Blue-Net-Team/2024-GuangDong-Engineering-practice-and-innovation-ability-competition---Don-t-count-on-us/Pic/1.png

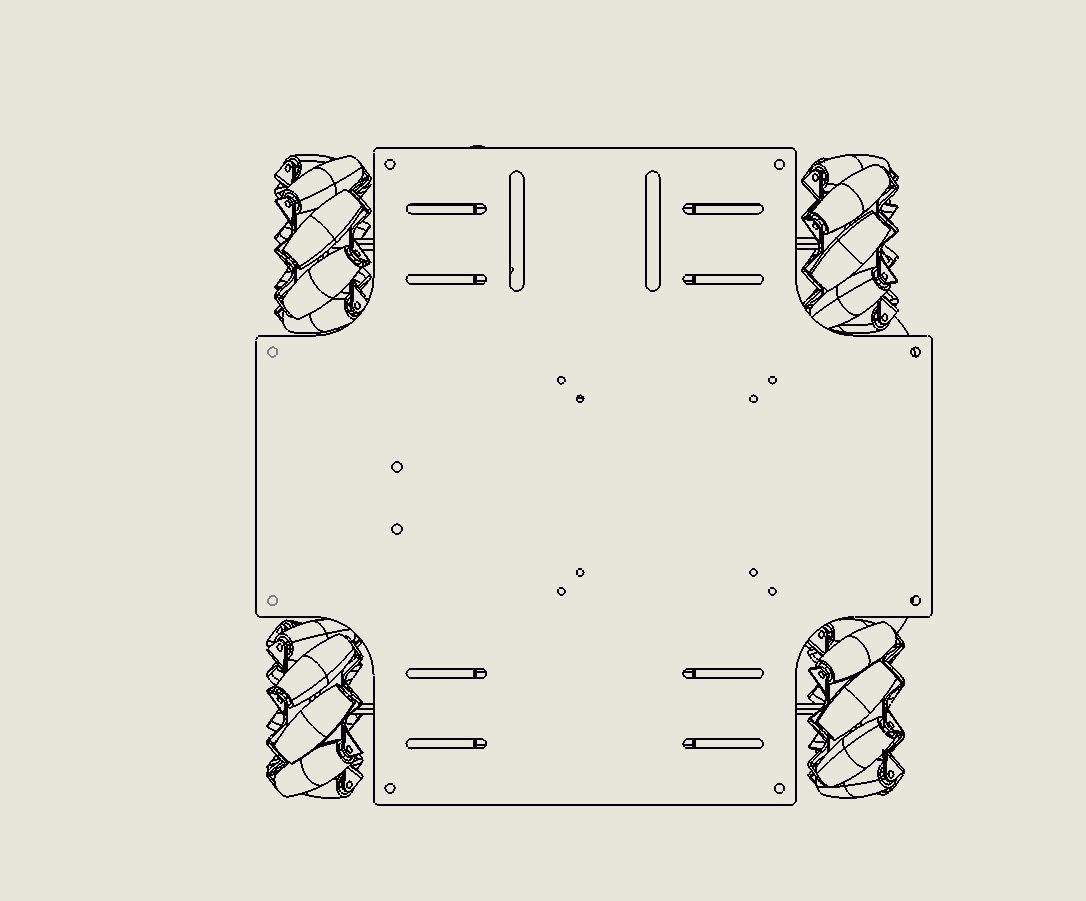
Pic/1.png
