Blue-Net-Team/2024-GuangDong-Engineering-practice-and-innovation-ability-competition---Don-t-count-on-us/Pic/3.png

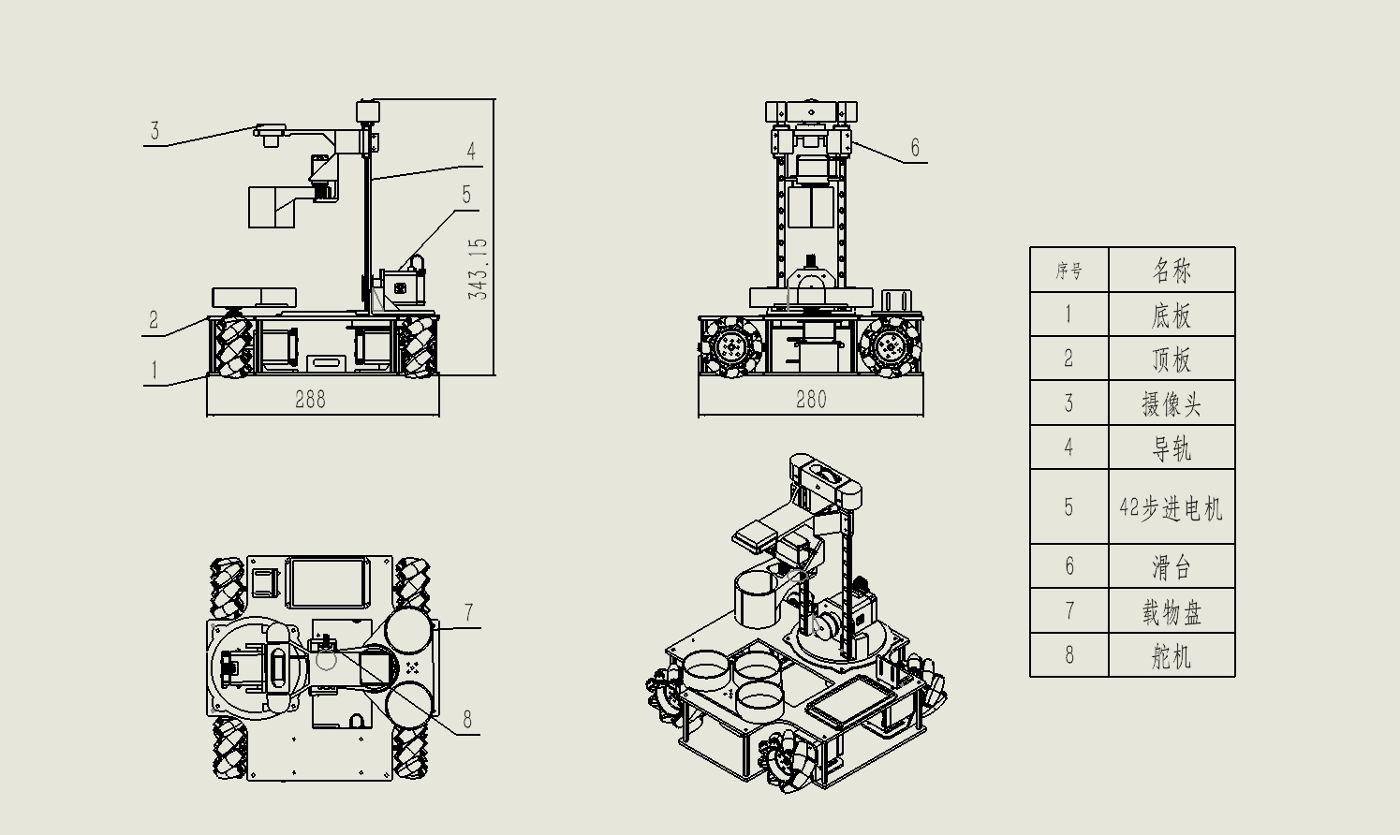
Pic/3.png
