Blue-Net-Team/2024-GuangDong-Engineering-practice-and-innovation-ability-competition---Don-t-count-on-us/Structure/MGN9-250.SLDASM

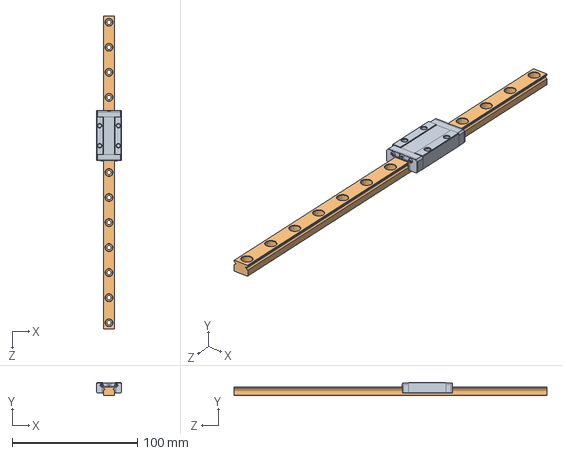
[picture p6: CAD file, 2024-07-28]
Structure/MGN9-250.SLDASM
20.0 x 10.0 x 250.0 mm
滑轨
滑台
