Blue-Net-Team/2024-GuangDong-Engineering-practice-and-innovation-ability-competition---Don-t-count-on-us/Structure/同步轮.SLDPRT

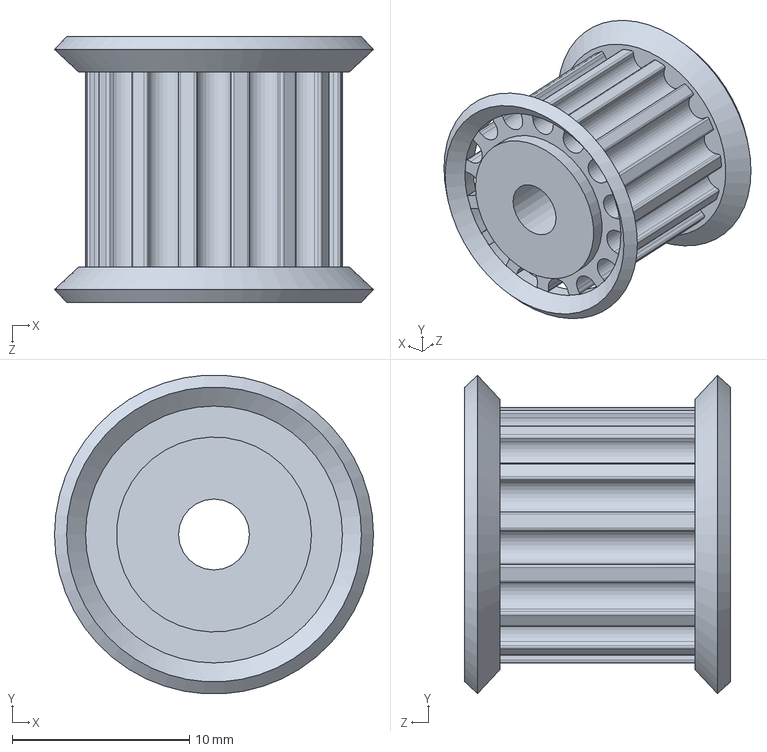
[picture p20: CAD file, 2024-07-28]
Structure/同步轮.SLDPRT
18.0 x 18.0 x 15.0 mm
