Blue-Net-Team/2024-GuangDong-Engineering-practice-and-innovation-ability-competition---Don-t-count-on-us/Structure/便携爪子初始加长.SLDPRT

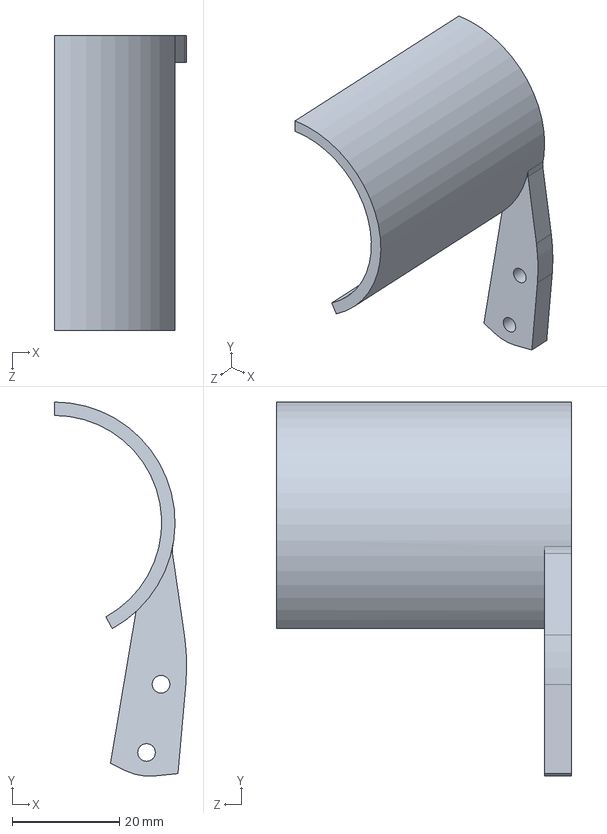
[picture p21: CAD file, 2024-07-28]
Structure/便携爪子初始加长.SLDPRT
24.7 x 69.7 x 55.0 mm
