Blue-Net-Team/2024-GuangDong-Engineering-practice-and-innovation-ability-competition---Don-t-count-on-us/Structure/轴承.SLDPRT

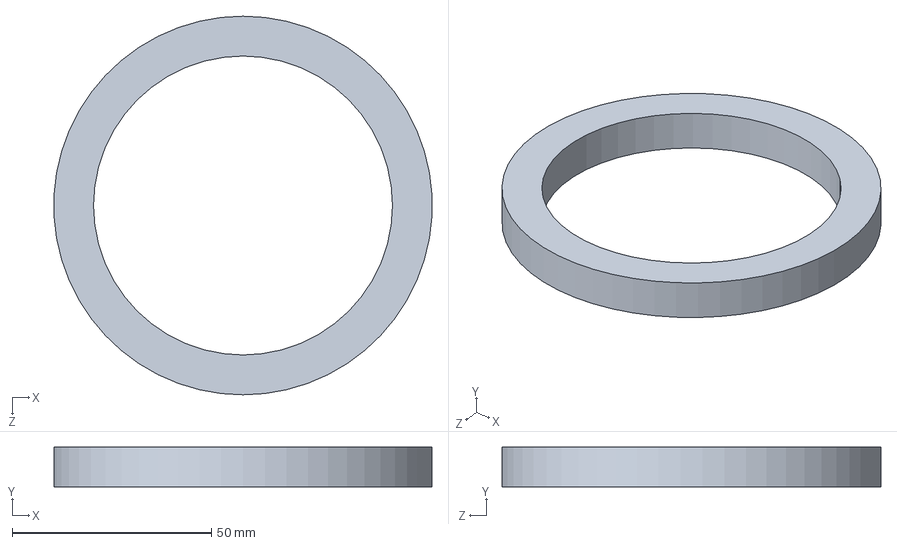
[picture p22: CAD file, 2024-07-28]
Structure/轴承.SLDPRT
94.8 x 10.0 x 95.0 mm
