Blue-Net-Team/2024-GuangDong-Engineering-practice-and-innovation-ability-competition---Don-t-count-on-us/Structure/爪子2.SLDPRT

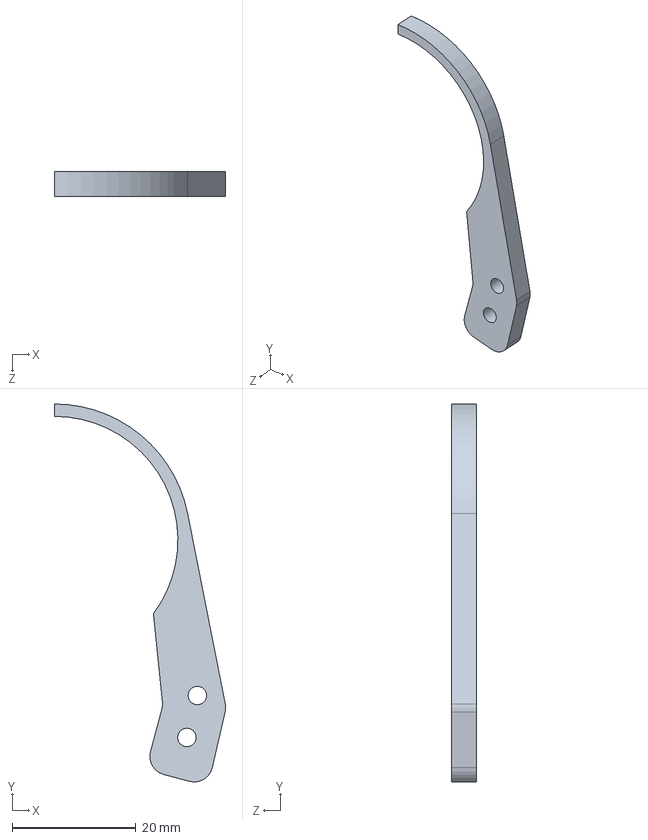
[picture p24: CAD file, 2024-07-28]
Structure/爪子2.SLDPRT
27.7 x 61.2 x 4.00 mm
