Blue-Net-Team/2024-GuangDong-Engineering-practice-and-innovation-ability-competition---Don-t-count-on-us/Structure/电池支架2.SLDPRT

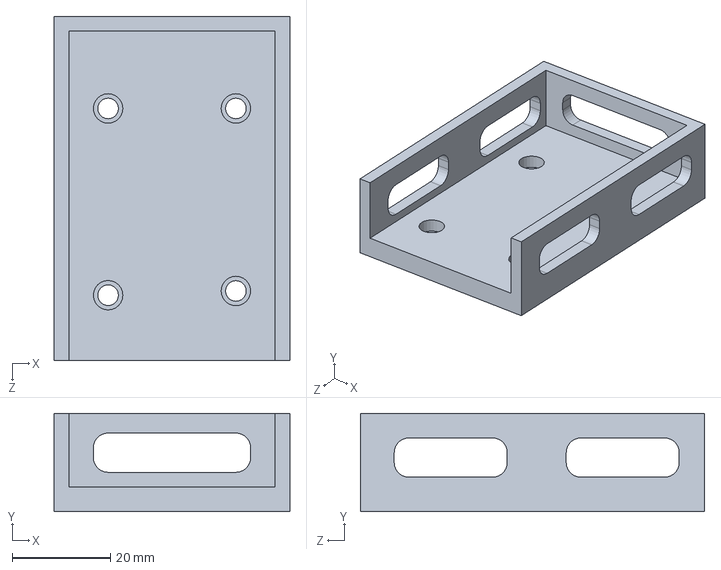
[picture p25: CAD file, 2024-07-28]
Structure/电池支架2.SLDPRT
48.0 x 20.0 x 70.0 mm
