Blue-Net-Team/2024-GuangDong-Engineering-practice-and-innovation-ability-competition---Don-t-count-on-us/Structure/上板.SLDPRT

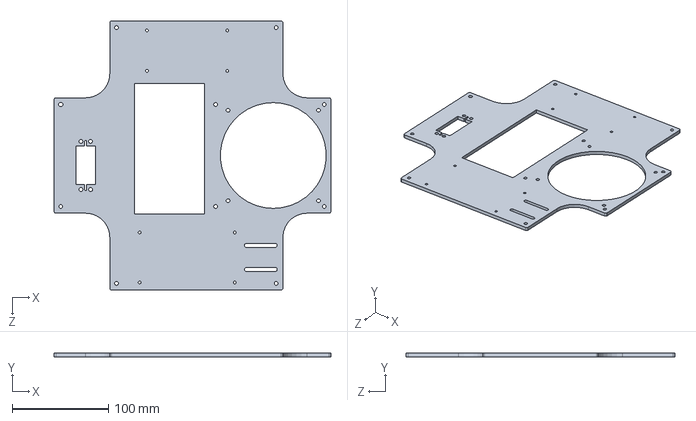
[picture p26: CAD file, 2024-07-28]
Structure/上板.SLDPRT
288.0 x 4.00 x 280.0 mm
