Blue-Net-Team/2024-GuangDong-Engineering-practice-and-innovation-ability-competition---Don-t-count-on-us/Structure/便携爪子初始.SLDPRT

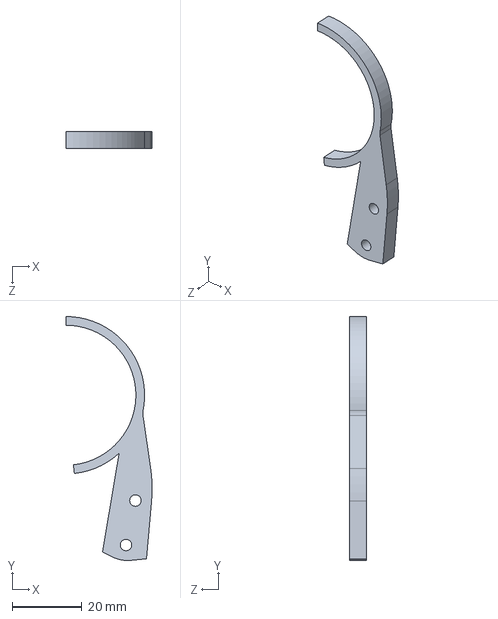
[picture p27: CAD file, 2024-07-28]
Structure/便携爪子初始.SLDPRT
24.6 x 69.7 x 5.00 mm
