Blue-Net-Team/2024-GuangDong-Engineering-practice-and-innovation-ability-competition---Don-t-count-on-us/Structure/云台顶盘.SLDPRT

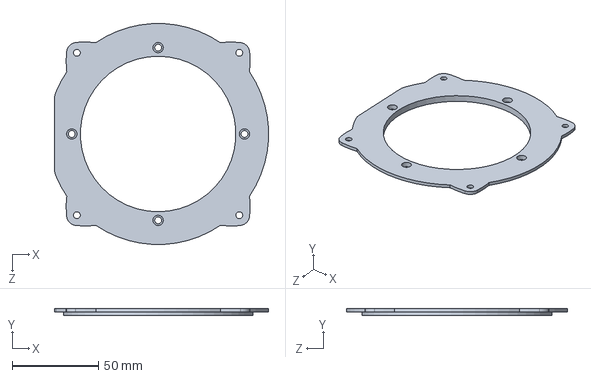
[picture p28: CAD file, 2024-07-28]
Structure/云台顶盘.SLDPRT
123.9 x 4.00 x 127.8 mm
