Blue-Net-Team/2024-GuangDong-Engineering-practice-and-innovation-ability-competition---Don-t-count-on-us/Structure/摄像头固定支架.SLDPRT

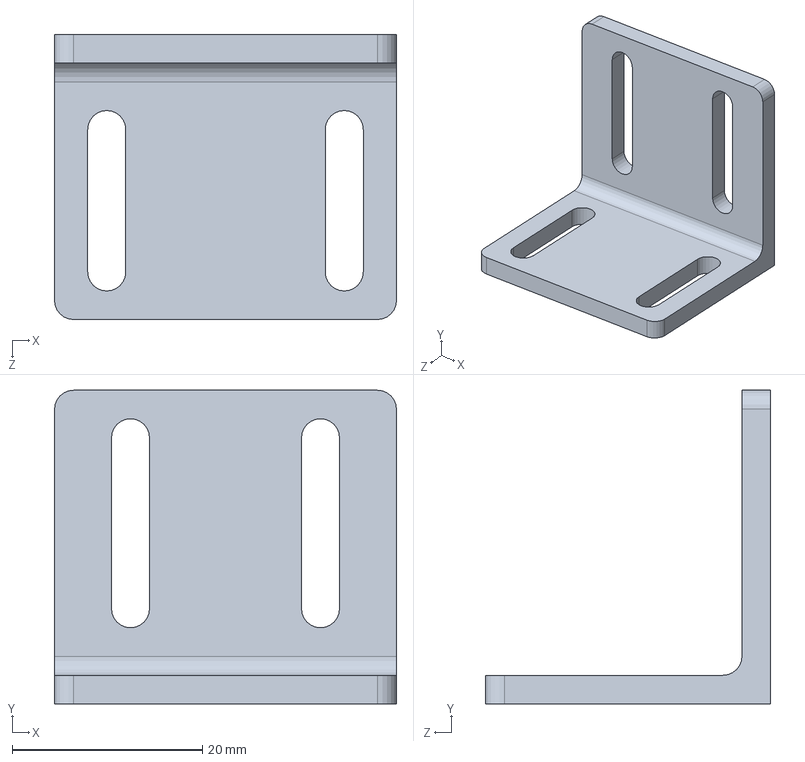
[picture p29: CAD file, 2024-07-28]
Structure/摄像头固定支架.SLDPRT
36.0 x 33.0 x 30.0 mm
