Blue-Net-Team/2024-GuangDong-Engineering-practice-and-innovation-ability-competition---Don-t-count-on-us/Structure/舵机.SLDPRT

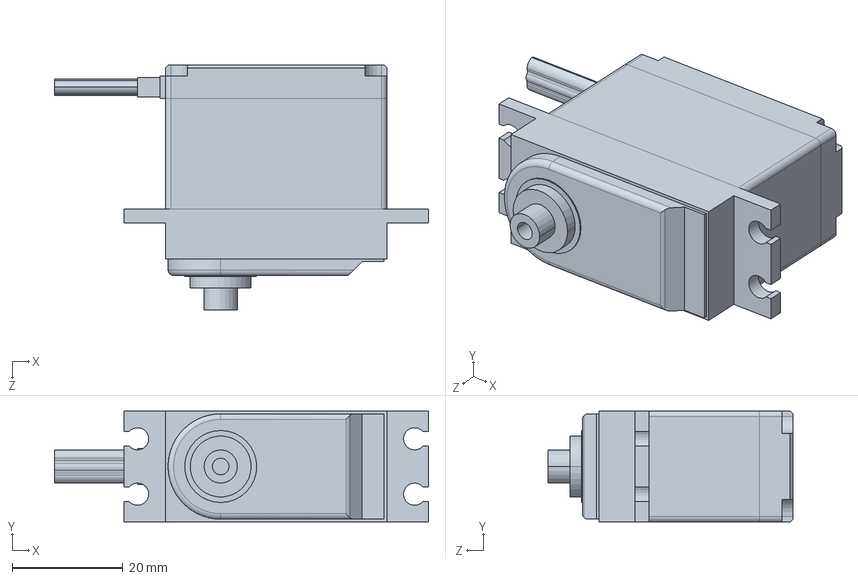
[picture p30: CAD file, 2024-07-28]
Structure/舵机.SLDPRT
67.5 x 20.0 x 44.2 mm
