Blue-Net-Team/2024-GuangDong-Engineering-practice-and-innovation-ability-competition---Don-t-count-on-us/Structure/树莓派固定2.SLDPRT

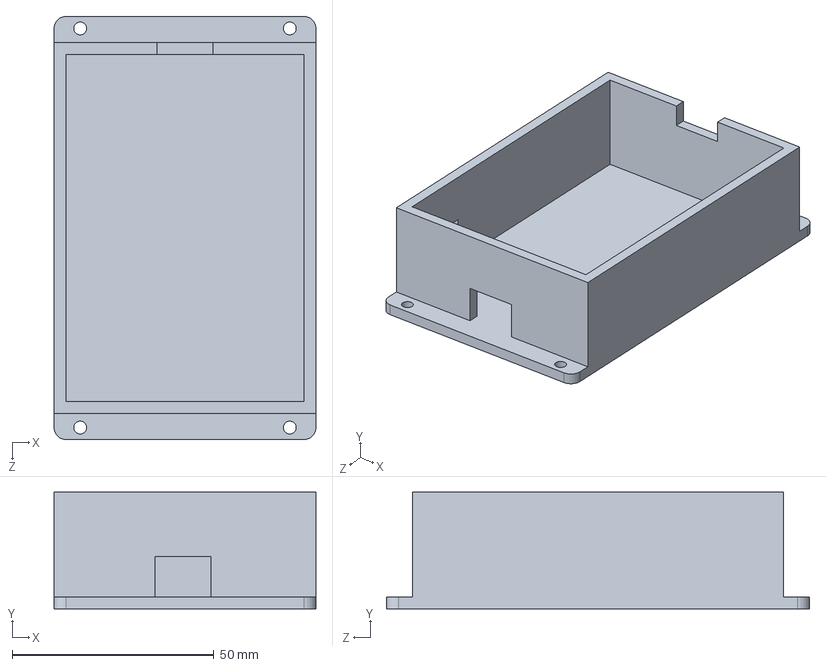
[picture p31: CAD file, 2024-07-28]
Structure/树莓派固定2.SLDPRT
65.0 x 29.0 x 105.0 mm
