Blue-Net-Team/2024-GuangDong-Engineering-practice-and-innovation-ability-competition---Don-t-count-on-us/Structure/下固定板.SLDPRT

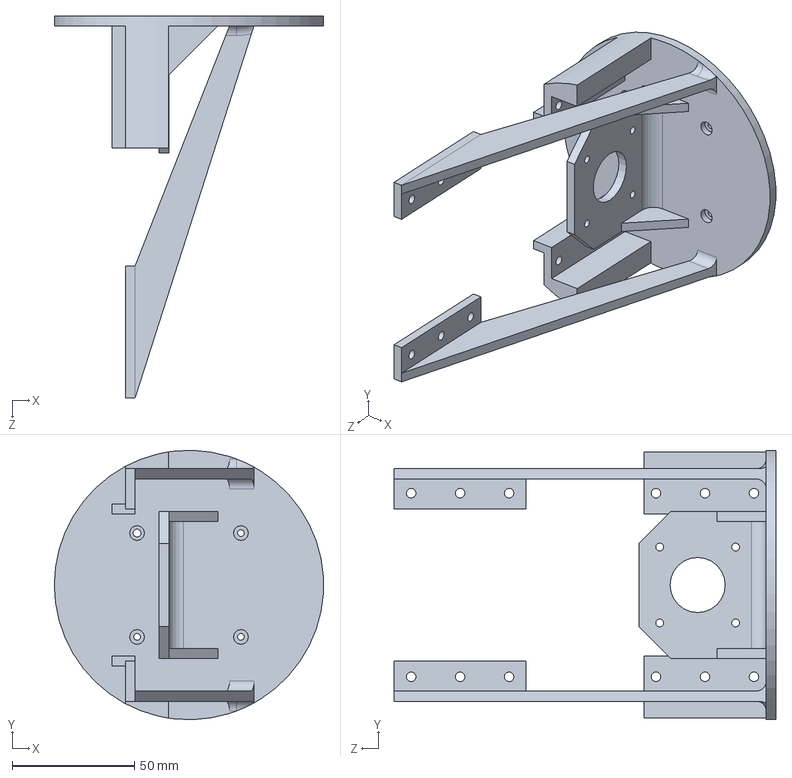
[picture p32: CAD file, 2024-07-28]
Structure/下固定板.SLDPRT
110.0 x 109.9 x 156.0 mm
