Blue-Net-Team/2024-GuangDong-Engineering-practice-and-innovation-ability-competition---Don-t-count-on-us/Structure/机械爪右便携支架.SLDPRT

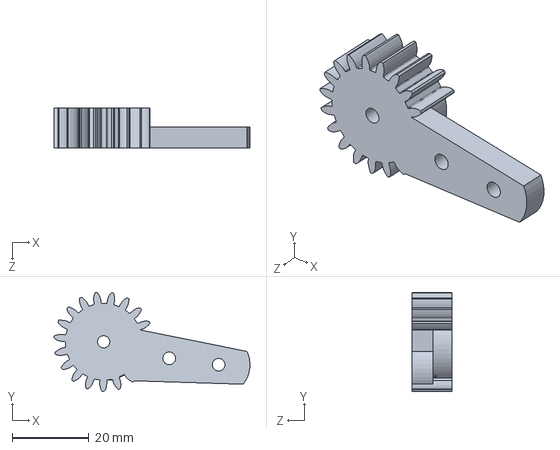
[picture p33: CAD file, 2024-07-28]
Structure/机械爪右便携支架.SLDPRT
51.1 x 25.9 x 10.4 mm
