Blue-Net-Team/2024-GuangDong-Engineering-practice-and-innovation-ability-competition---Don-t-count-on-us/Structure/上同步轮固定.SLDPRT

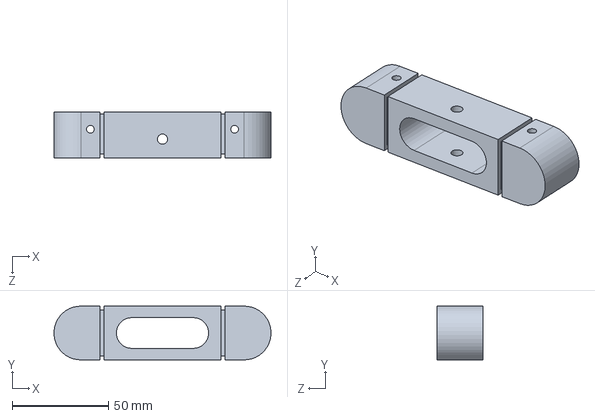
[picture p34: CAD file, 2024-07-28]
Structure/上同步轮固定.SLDPRT
112.9 x 28.0 x 24.0 mm
