Blue-Net-Team/2024-GuangDong-Engineering-practice-and-innovation-ability-competition---Don-t-count-on-us/Structure/底板.SLDPRT

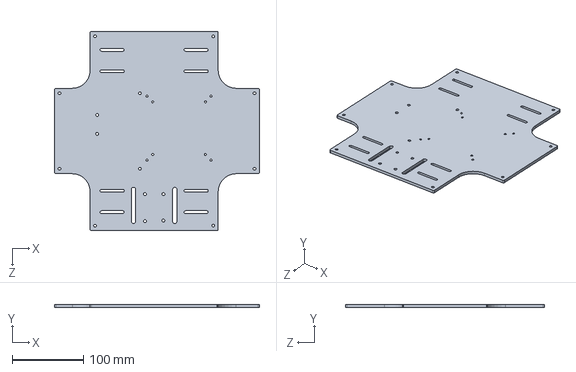
[picture p35: CAD file, 2024-07-28]
Structure/底板.SLDPRT
288.0 x 4.00 x 280.0 mm
