Blue-Net-Team/2024-GuangDong-Engineering-practice-and-innovation-ability-competition---Don-t-count-on-us/Structure/滑台.SLDPRT

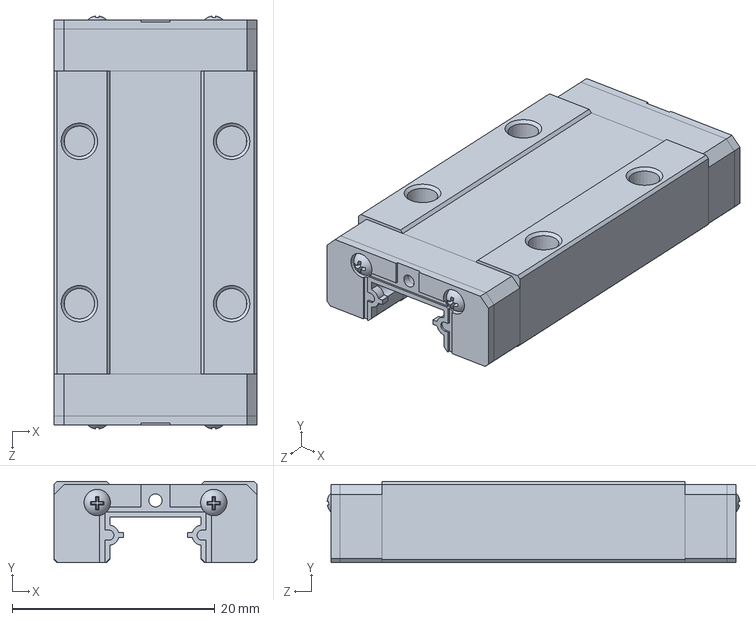
[picture p36: CAD file, 2024-07-28]
Structure/滑台.SLDPRT
20.0 x 8.00 x 40.7 mm
