Blue-Net-Team/2024-GuangDong-Engineering-practice-and-innovation-ability-competition---Don-t-count-on-us/Structure/机械爪左初始.SLDPRT

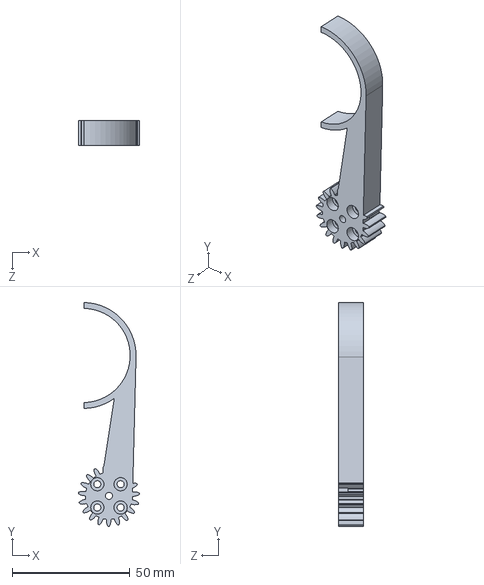
[picture p37: CAD file, 2024-07-28]
Structure/机械爪左初始.SLDPRT
25.9 x 95.1 x 10.5 mm
