Blue-Net-Team/2024-GuangDong-Engineering-practice-and-innovation-ability-competition---Don-t-count-on-us/Structure/升降链接6.SLDPRT

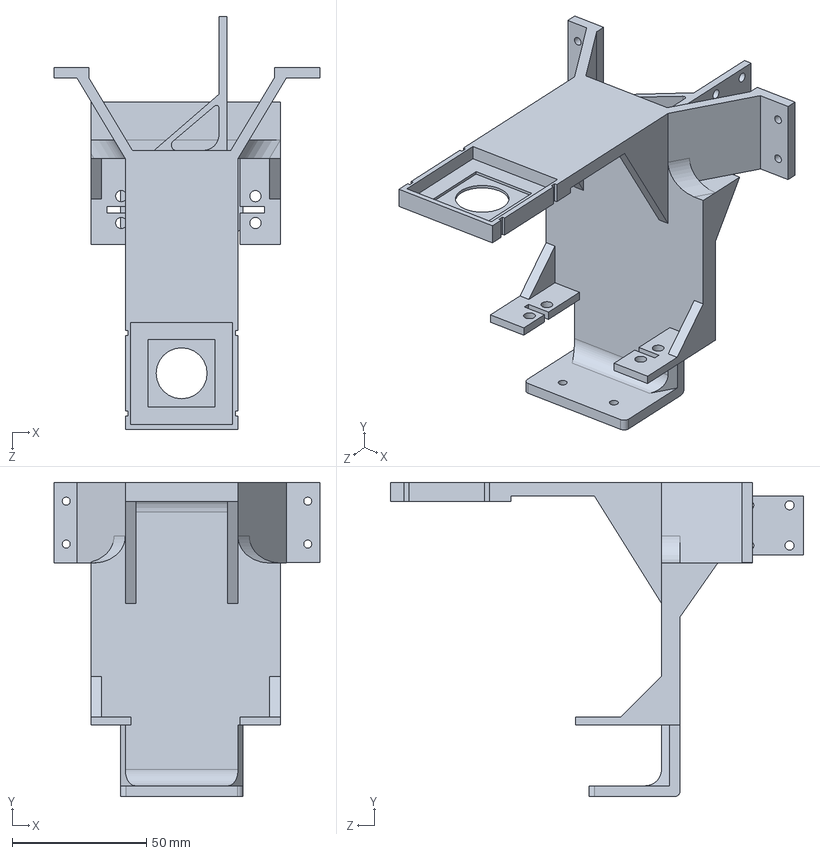
[picture p38: CAD file, 2024-07-28]
Structure/升降链接6.SLDPRT
99.0 x 117.0 x 154.0 mm
