Blue-Net-Team/2024-GuangDong-Engineering-practice-and-innovation-ability-competition---Don-t-count-on-us/Structure/二维码模块固定板.SLDPRT

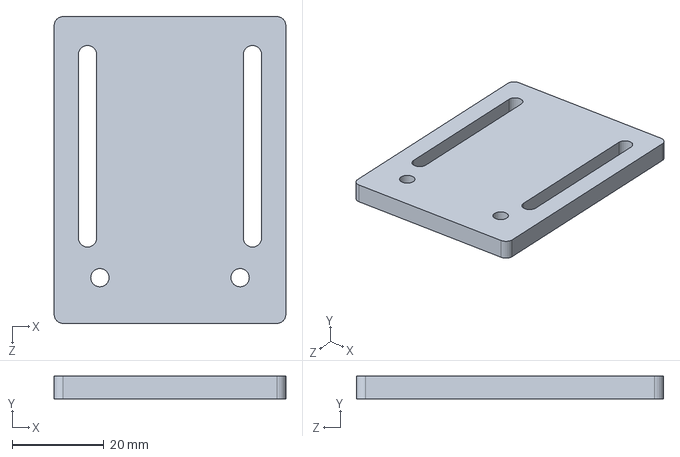
[picture p39: CAD file, 2024-07-28]
Structure/二维码模块固定板.SLDPRT
50.6 x 5.00 x 67.0 mm
