Blue-Net-Team/2024-GuangDong-Engineering-practice-and-innovation-ability-competition---Don-t-count-on-us/Structure/机械爪右初始.SLDPRT

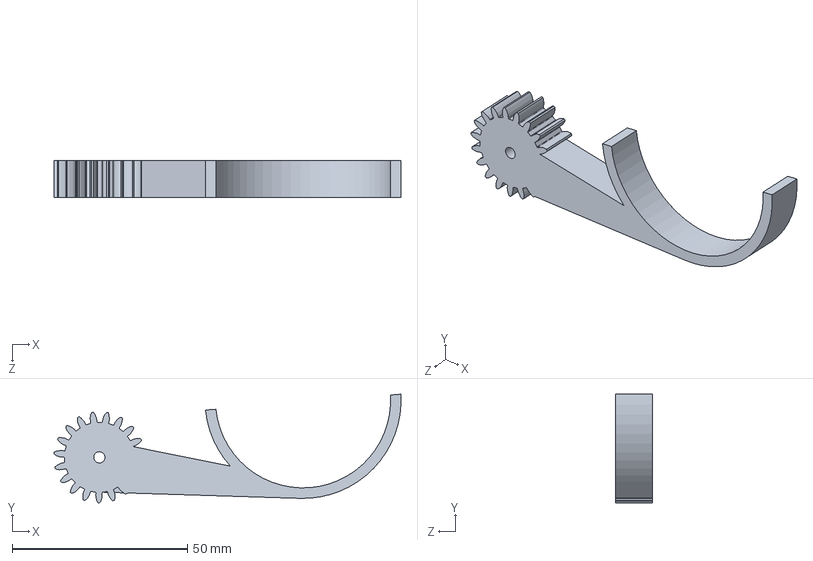
[picture p40: CAD file, 2024-07-28]
Structure/机械爪右初始.SLDPRT
99.1 x 31.0 x 10.4 mm
