Blue-Net-Team/2024-GuangDong-Engineering-practice-and-innovation-ability-competition---Don-t-count-on-us/Structure/二维码模块上层固定架2.SLDPRT

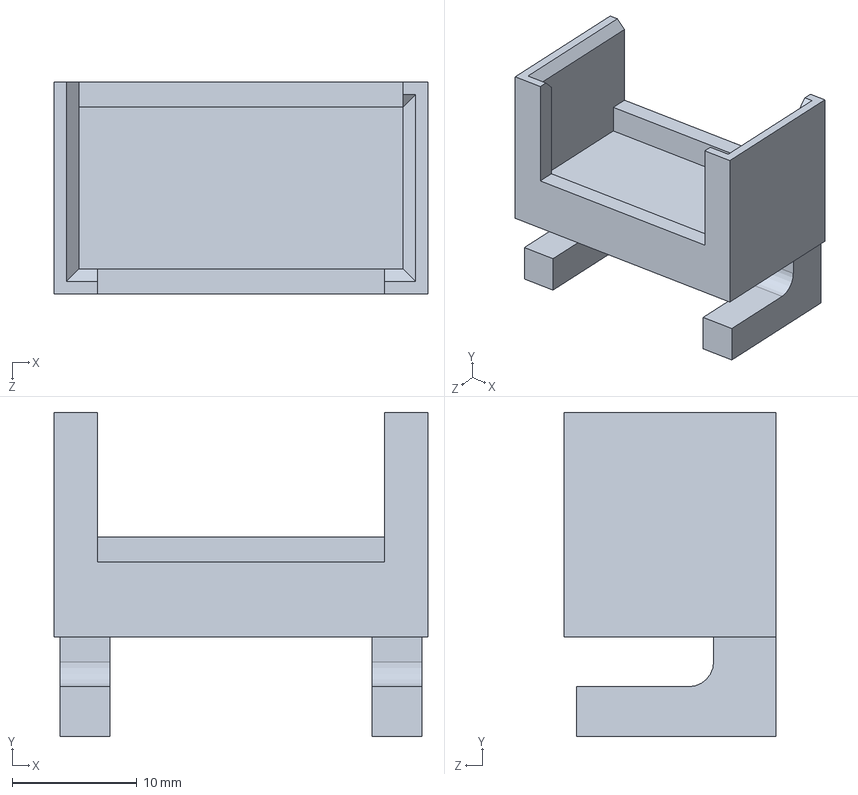
[picture p41: CAD file, 2024-07-28]
Structure/二维码模块上层固定架2.SLDPRT
30.0 x 26.0 x 17.0 mm
