Blue-Net-Team/2024-GuangDong-Engineering-practice-and-innovation-ability-competition---Don-t-count-on-us/Structure/旋转底层.SLDPRT

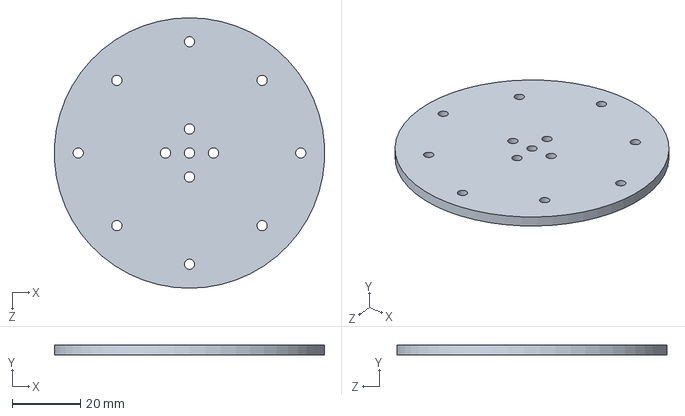
[picture p42: CAD file, 2024-07-28]
Structure/旋转底层.SLDPRT
78.9 x 3.00 x 79.0 mm
