Blue-Net-Team/2024-GuangDong-Engineering-practice-and-innovation-ability-competition---Don-t-count-on-us/Structure/滑轨.SLDPRT

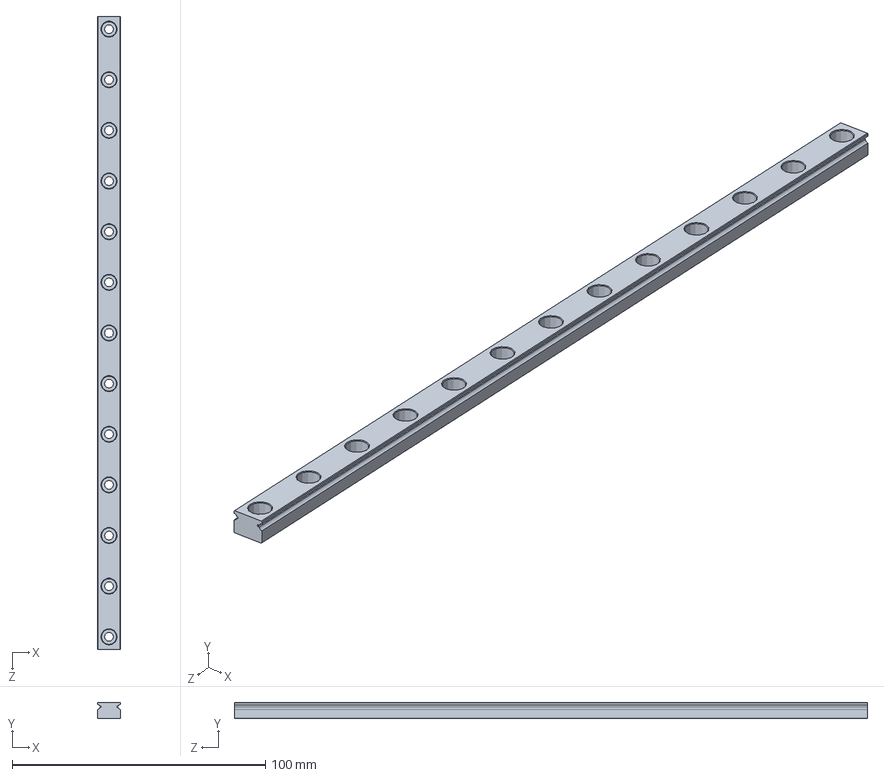
[picture p43: CAD file, 2024-07-28]
Structure/滑轨.SLDPRT
9.00 x 6.50 x 250.0 mm
