Blue-Net-Team/2024-GuangDong-Engineering-practice-and-innovation-ability-competition---Don-t-count-on-us/Structure/法兰盘.SLDPRT

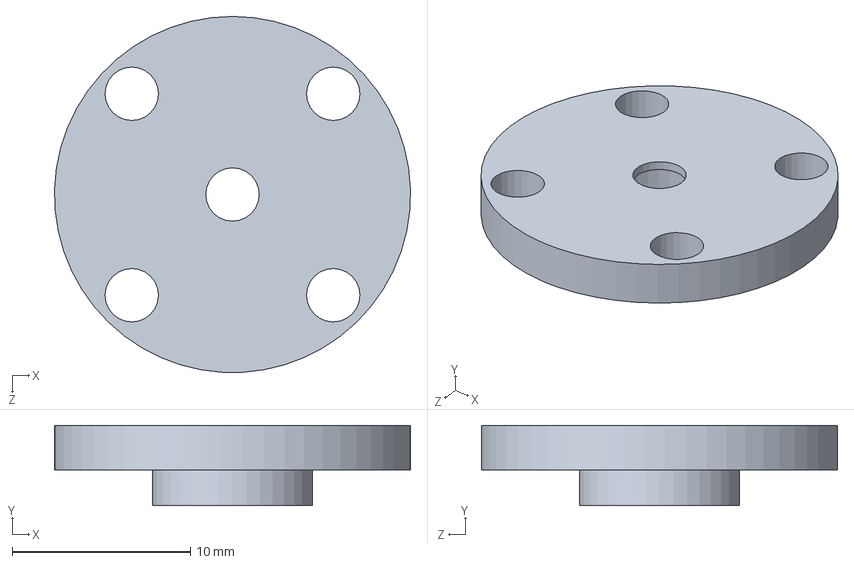
[picture p44: CAD file, 2024-07-28]
Structure/法兰盘.SLDPRT
20.0 x 4.50 x 20.0 mm
