Blue-Net-Team/2024-GuangDong-Engineering-practice-and-innovation-ability-competition---Don-t-count-on-us/Structure/物料.SLDPRT

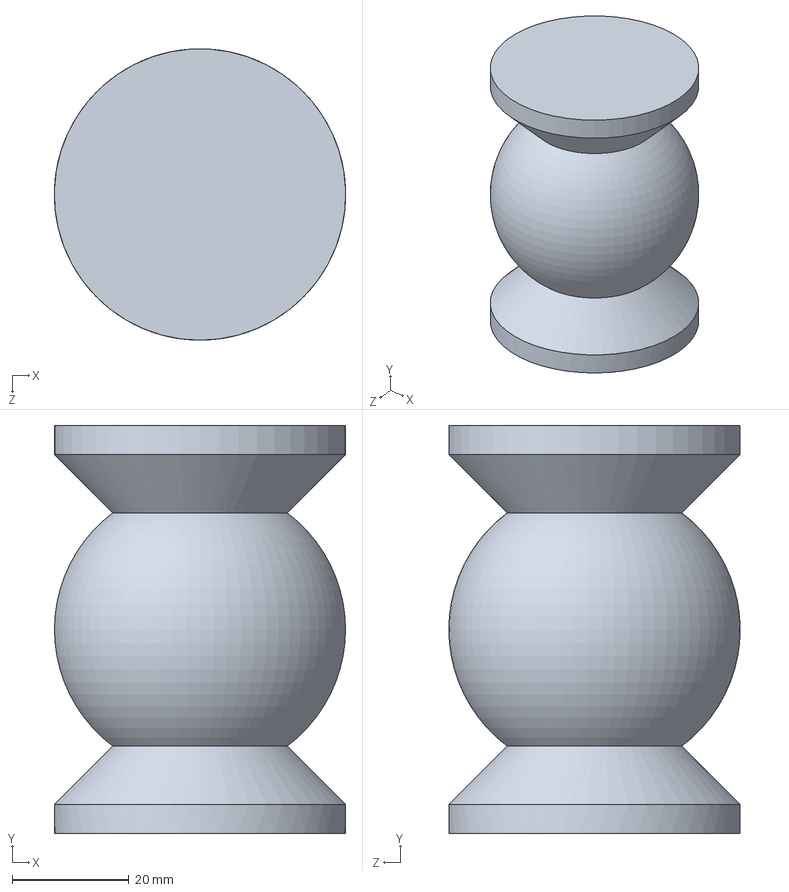
[picture p45: CAD file, 2024-07-28]
Structure/物料.SLDPRT
50.0 x 70.0 x 50.0 mm
