Blue-Net-Team/2024-GuangDong-Engineering-practice-and-innovation-ability-competition---Don-t-count-on-us/Structure/机械爪左2.SLDPRT

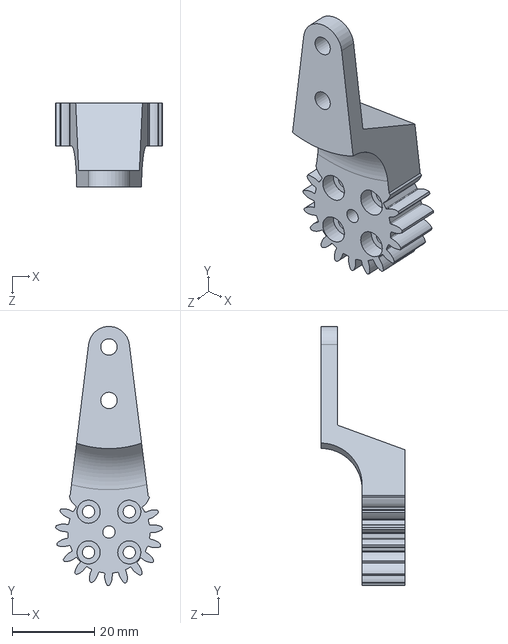
[picture p46: CAD file, 2024-07-28]
Structure/机械爪左2.SLDPRT
25.9 x 63.0 x 20.5 mm
