Blue-Net-Team/2024-GuangDong-Engineering-practice-and-innovation-ability-competition---Don-t-count-on-us/Structure/机械爪2.SLDASM

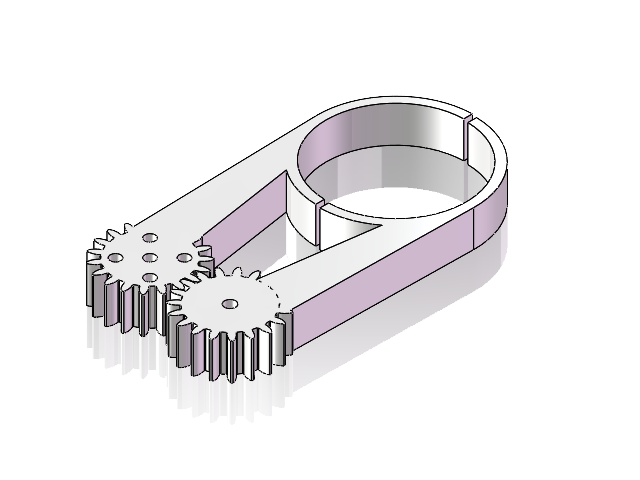
[picture p47: CAD file, 2024-07-28]
Structure/机械爪2.SLDASM
机械爪左2
机械爪右2
