Blue-Net-Team/2024-GuangDong-Engineering-practice-and-innovation-ability-competition---Don-t-count-on-us/Structure/42步进电机.SLDASM

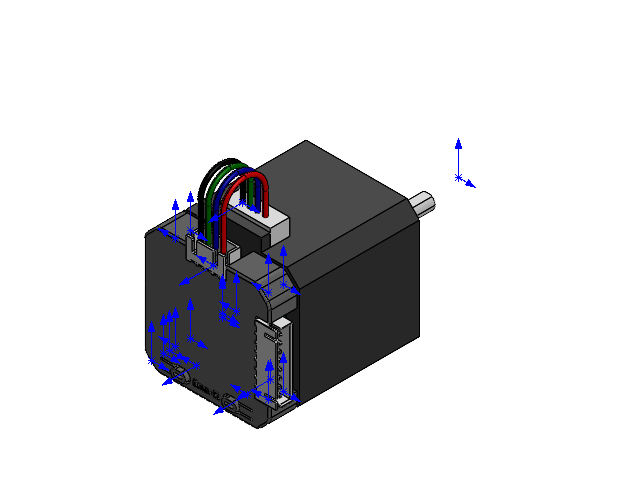
[picture p48: CAD file, 2024-07-28]
Structure/42步进电机.SLDASM
ts-1145a-b-a_White.step.STEP x 2
User_Library-XH2_54-4P-AW.step.STEP
XH2.54-8P_H-0.step.STEP
Extruded.step.STEP
Extruded-1.step.STEP
42_STEPPER_MOTOR.STEP
SHIM_3x7x3.STEP x 4
M3x6mm_Phillips.STEP x 4
ZDT_X42_V1.2.STEP
WIRE_2.54.STEP
