Blue-Net-Team/2024-GuangDong-Engineering-practice-and-innovation-ability-competition---Don-t-count-on-us/Structure/mecanum wheel.SLDASM

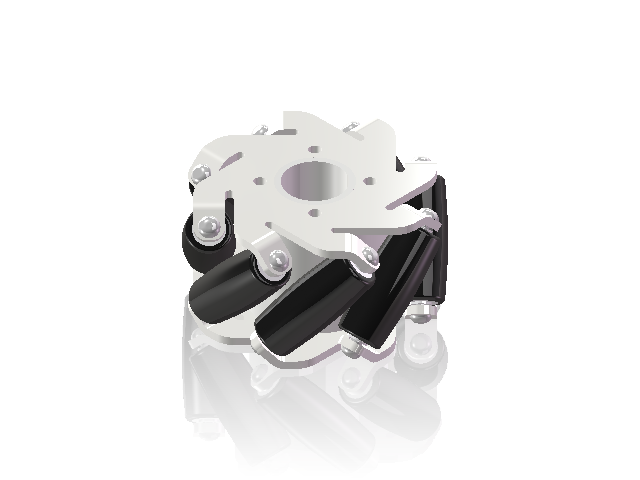
[picture p49: CAD file, 2024-07-28]
Structure/mecanum wheel.SLDASM
FRAME1.step
ROLLER.step x 8
Component4.step
bracket.step x 8
FRAME1 (1).step
bracket (1).step x 8
rod.step x 8
