Blue-Net-Team/2024-GuangDong-Engineering-practice-and-innovation-ability-competition---Don-t-count-on-us/Vision/detector.py

import json
import cv2
import numpy as np


class ColorDetector(object):
    """颜色识别器
    * 通过调节trackbar来调节颜色阈值
    * 使用detect方法来识别颜色，得到二值化过滤后的图像数据
    * 使用draw_rectangle方法来在图像上绘制矩形框，传入的应该是二值化过滤后的图像数据"""
    def __init__(self) -> None:
        """初始化"""
        # region 初始颜色阈值
        self.low_h = 0
        self.low_s = 0
        self.low_v = 0

        self.high_h = 180
        self.high_s = 255
        self.high_v = 255

        self.minR = 35
        self.maxR = 4500
        # endregion

    def set_threshold(self, _threshold:tuple[list[int], list[int]]) -> None:
        """设置颜色阈值
        * _threshold: 传入的颜色阈值"""
        self.low_h = _threshold[0][0]
        self.low_s = _threshold[0][1]
        self.low_v = _threshold[0][2]

        self.high_h = _threshold[1][0]
        self.high_s = _threshold[1][1]
        self.high_v = _threshold[1][2]

    def createTrackbar(self,_id:int=0):
        """调出trackbar
        * id: 识别器的id的id"""
        # region 创建trackbar
        cv2.namedWindow(f'Color and circle trackbar{_id}', cv2.WINDOW_NORMAL)
        cv2.createTrackbar('low_h', f'Color and circle trackbar{_id}', self.low_h, 180, self.call_back_low_h)
        cv2.createTrackbar('high_h', f'Color and circle trackbar{_id}', self.high_h, 180, self.call_back_high_h)
        cv2.createTrackbar('low_s', f'Color and circle trackbar{_id}', self.low_s, 255, self.call_back_low_s)
        cv2.createTrackbar('high_s', f'Color and circle trackbar{_id}', self.high_s, 255, self.call_back_high_s)
        cv2.createTrackbar('low_v', f'Color and circle trackbar{_id}', self.low_v, 255, self.call_back_low_v)
        cv2.createTrackbar('high_v', f'Color and circle trackbar{_id}', self.high_v, 255, self.call_back_high_v)
        cv2.createTrackbar('minR', f'Color and circle trackbar{_id}', self.minR, 100, self.call_back_minarea)
        cv2.createTrackbar('maxR', f'Color and circle trackbar{_id}', self.maxR, 150, self.call_back_maxarea)
        # endregion
        pass

    # region trackbar回调函数
    def callback(self, x):
        pass

    def call_back_low_h(self, low_h):
        self.low_h = low_h
    
    def call_back_high_h(self, high_h):
        self.high_h = high_h

    def call_back_low_s(self, low_s):
        self.low_s = low_s

    def call_back_high_s(self, high_s):
        self.high_s = high_s

    def call_back_low_v(self, low_v):
        self.low_v = low_v

    def call_back_high_v(self, high_v):
        self.high_v = high_v

    def call_back_minarea(self, minarea):
        self.minR = minarea

    def call_back_maxarea(self, maxarea):
        self.maxR = maxarea
    # endregion

    def filter(self, img:cv2.typing.MatLike|None, _iteration1:int=1, _iteration2:int=1):
        """颜色识别 二值化滤波
        * img: 传入的图像数据
        * iteration1: 闭运算的迭代次数
        * iteration2: 开运算的迭代次数
        * 返回值：二值化过滤后的图像数据"""
        if img is None:return None
        _shape = img.shape
        try:
            hsv = cv2.cvtColor(img, cv2.COLOR_BGR2HSV)				# 将BGR图像转换成HSV图像
        except:
            return np.zeros((_shape[0], _shape[1]), np.uint8)

        low = np.array([self.low_h, self.low_s, self.low_v])		# 低阈值
        high = np.array([self.high_h, self.high_s, self.high_v])	# 高阈值

        mask = cv2.inRange(hsv, low, high)						# 通过阈值过滤图像，将在阈值范围内的像素点设置为255，不在阈值范围内的像素点设置为0
        kernel = np.ones((3, 3), np.uint8)						# 创建一个5*5的矩阵，矩阵元素全为1
        res = cv2.morphologyEx(mask, cv2.MORPH_CLOSE, kernel, iterations=_iteration1)   # 闭运算
        # 开运算
        res = cv2.morphologyEx(res, cv2.MORPH_OPEN, kernel, iterations=_iteration2)
        return res

    def draw_rectangle(self, img:cv2.typing.MatLike): 
        """在图像上绘制矩形框
        * img: 传入的二值化图像数据
        * 返回值：绘制矩形框后的图像数据，矩形框的坐标"""
        lst = []
        for cnt in ColorDetector.__get_edge(img):										# 遍历轮廓数据
            x, y, w, h = cv2.boundingRect(cnt)						# 获取矩形框的坐标和宽高

            if (self.minR > w*h or w*h > self.maxR):
                continue
            if h/w > 1.5:
                continue
            cv2.rectangle(img, (x, y), (x + w, y + h), (0, 255, 0), 2)	# 在图像上绘制矩形框
            lst.append((x, y, x + w, y + h))
        return img, lst
    
    def draw_cycle(self, img:cv2.typing.MatLike) -> tuple[cv2.typing.MatLike, list[tuple[tuple[int, int], int]]]:
        """在图像上绘制圆形
        * img: 传入的二值化图像数据
        * 返回值：绘制圆形后的图像数据，圆形的坐标(圆心，半径),如果没有识别到圆形，图像不会绘制圆形，并且返回空列表"""
        lst = []
        for cnt in ColorDetector.__get_edge(img):										# 遍历轮廓数据
            (x, y), radius = cv2.minEnclosingCircle(cnt)        # 获取最小外接圆的圆心坐标和半径
            center = (int(x), int(y))
            radius = int(radius)
            area = cv2.contourArea(cnt)
            if (radius < self.minR or radius > self.maxR):
                continue
            # cv2.circle(img, center, radius, (0, 255, 0), 2)
            lst.append((center, radius))
        return img, lst
    
    @staticmethod
    def __get_edge(img:cv2.typing.MatLike):
        """静态函数获取边缘
        * img: 传入的图像数据
        返回值：边缘图像"""
        # conuours是轮廓，hierarchy是轮廓的层级
        contours, _ = cv2.findContours(img, cv2.RETR_TREE, cv2.CHAIN_APPROX_SIMPLE)
        return contours
    
    def __del__(self):
        """析构函数"""
        cv2.destroyAllWindows()
        pass


class LineDetector(object):
    """直线识别器"""
    def __init__(self) -> None:
        self.minval = 0
        self.maxval = 255

    def set_threshold(self, _threshold:tuple[int, int]) -> None:
        """设置直线识别的阈值
        * _threshold: 传入的阈值"""
        self.minval = _threshold[0]
        self.maxval = _threshold[1]

    def createTrackbar(self,_id:int=0) -> None:
        cv2.namedWindow(f'Line trackbar{_id}', cv2.WINDOW_NORMAL)
        cv2.createTrackbar('minval', f'Line trackbar{_id}', self.minval, 255, self.minval_callback)
        cv2.createTrackbar('maxval', f'Line trackbar{_id}', self.maxval, 255, self.maxval_callback)

    # region trackbar回调函数
    def minval_callback(self, x):
        self.minval = x

    def maxval_callback(self, x):
        self.maxval = x
    # endregion

    def get_angle(self, 
                  _img0:cv2.typing.MatLike|None, 
                  ifdubug:bool=False, 
                  close:int=1, 
                  _open:int=1,
                  rho:int|float=1,
                  thre:int=200):
        """获取直线的角度
        * img: 传入的图像数据
        * ifdubug: 是否调试"""
        if _img0 is None:return None, None
        _img1 = _img0.copy()
        # 转换为灰度图
        gray = cv2.cvtColor(_img1, cv2.COLOR_BGR2GRAY)
        # 使用Canny算法进行边缘检测
        edges = cv2.Canny(gray, self.minval, self.maxval, apertureSize=3)
        # 闭运算
        edges = cv2.morphologyEx(edges, cv2.MORPH_CLOSE, (5, 5), iterations=close)        # type:ignore
        # 开运算
        edges = cv2.morphologyEx(edges, cv2.MORPH_OPEN, (5, 5), iterations=_open)        # type:ignore
        # 膨胀
        edges = cv2.dilate(edges, (3, 3), iterations=3)        # type:ignore
        if ifdubug: cv2.imshow('edges', edges)
        # 使用霍夫变换检测直线
        lines = cv2.HoughLines(edges, rho, np.pi / 180, thre)

        if lines is not None:       # 如果检测到直线
            for rho, theta in lines[0]:
                a = np.cos(theta)
                b = np.sin(theta)
                x0 = a * rho
                y0 = b * rho
                x1 = int(x0 + 1000 * (-b))
                y1 = int(y0 + 1000 * (a))
                x2 = int(x0 - 1000 * (-b))
                y2 = int(y0 - 1000 * (a))

                # 计算直线的斜率
                if x2 - x1 == 0:  # 避免除以零的错误
                    continue
                slope = (y2 - y1) / (x2 - x1)
                # 计算直线的角度（以度为单位）
                angle = np.arctan(slope) * 180 / np.pi
                # 将识别的线画出来
                cv2.line(_img1, (x1, y1), (x2, y2), (0, 0, 255), 2)
                return _img1, angle

        return _img1, None
        

class CircleDetector(object):
    """
    圆形识别器
    ----
    通过霍夫圆环检测算法检测圆环
    """
    def __init__(self) -> None:
        self.totalizer = 100
        self.maxval = 20
        self.mindist = 100
        self.minR = 0
        self.maxR = 400

    def createTrackbar(self,_id:int=0) -> None:
        cv2.namedWindow(f'Circle trackbar{_id}', cv2.WINDOW_NORMAL)
        cv2.createTrackbar('totalizer', f'Circle trackbar{_id}', self.totalizer, 255, self.totalizer_callback)
        cv2.createTrackbar('maxval', f'Circle trackbar{_id}', self.maxval, 70, self.maxval_callback)
        cv2.createTrackbar('mindist', f'Circle trackbar{_id}', self.mindist, 200, self.mindist_callback)
        cv2.createTrackbar('minR', f'Circle trackbar{_id}', self.minR, 1000, self.minR_callback)
        cv2.createTrackbar('maxR', f'Circle trackbar{_id}', self.maxR, 1000, self.maxR_callback)

    #region trackbar回调函数
    def totalizer_callback(self, x):
        self.minval = x

    def maxval_callback(self, x):
        self.maxval = x

    def mindist_callback(self, x):
        self.mindist = x

    def minR_callback(self, x):
        self.minR = x

    def maxR_callback(self, x):
        self.maxR = x
    #endregion
        
    def get_circle(self, img0:cv2.typing.MatLike):
        """
        获取圆环
        ----
        * img0: 传入的图像数据
        * 返回值：绘制圆环后的图像数据，圆环的坐标(圆心，半径)的二维数组
        """
        img = img0.copy()       # 深拷贝
        img = cv2.cvtColor(img, cv2.COLOR_BGR2GRAY)       # 转换为灰度图
        if self.totalizer == 0 or self.maxval == 0 or self.mindist == 0:
            return img, np.array([[]])
        circles = cv2.HoughCircles(img,
                                   cv2.HOUGH_GRADIENT,
                                   1,
                                   self.mindist,
                                   param1=self.maxval,
                                   param2=self.totalizer,
                                   minRadius=0,
                                   maxRadius=0)
        if circles is None:
            return img, np.array([[]])
        for circle in circles[0]:
            x, y, r = circle
            x, y, r = int(x), int(y), int(r)
            cv2.circle(img0, (x, y), r, (255, 0, 255), 2)        # 画圆
        return img0, circles[0]

# ------------------------------测试代码------------------------------
if __name__ == '__main__':
    line = LineDetector()
    cap = cv2.VideoCapture(0)

    # region 直线识别第一测试
    while True:
        img = cap.read()[1]
        angle = line.get_angle(img)
        if angle is not None:
            print(angle)
        cv2.imshow('img', img)
        if cv2.waitKey(1) == 27:
            break
    # endregion
        
    # region 直线识别第二测试
    """ y0 = 400
    while True:
        img = cap.read()[1]
        angle = line.get_distance(img, y0=y0)
        if angle is not None:
            print(angle)
        cv2.imshow('img', img)
        if cv2.waitKey(1) == 27:
            break """
    # endregion
    pass
