Blue-Net-Team/2024-GuangDong-Engineering-practice-and-innovation-ability-competition---Don-t-count-on-us/Embedded/HARDWARE/TIMER/tim2.c

#include "stm32f4xx.h"                  // Device header
#include "tim2.h"

void Timer2_Init(int arr, int psc)
{
	GPIO_InitTypeDef            GPIO_InitStructure;
	TIM_TimeBaseInitTypeDef     TIM_TimeBaseStructure;
	TIM_OCInitTypeDef           TIM_OCInitStructure;

  	RCC_APB1PeriphClockCmd(RCC_APB1Periph_TIM2, ENABLE);
	RCC_AHB1PeriphClockCmd(RCC_AHB1Periph_GPIOA, ENABLE);

  	GPIO_PinAFConfig(GPIOA, GPIO_PinSource0, GPIO_AF_TIM2);
	GPIO_PinAFConfig(GPIOA, GPIO_PinSource1, GPIO_AF_TIM2);
	GPIO_PinAFConfig(GPIOA, GPIO_PinSource2, GPIO_AF_TIM2);
	GPIO_PinAFConfig(GPIOA, GPIO_PinSource3, GPIO_AF_TIM2); 

  	GPIO_InitStructure.GPIO_Pin = GPIO_Pin_0 | GPIO_Pin_1 | GPIO_Pin_2 | GPIO_Pin_3 ;
	GPIO_InitStructure.GPIO_Mode = GPIO_Mode_AF;
	GPIO_InitStructure.GPIO_Speed = GPIO_Speed_100MHz;
	GPIO_InitStructure.GPIO_OType = GPIO_OType_PP;
	GPIO_InitStructure.GPIO_PuPd = GPIO_PuPd_UP;
	GPIO_Init(GPIOA, &GPIO_InitStructure);

	TIM_TimeBaseStructure.TIM_Prescaler = psc;
	TIM_TimeBaseStructure.TIM_CounterMode = TIM_CounterMode_Up;
	TIM_TimeBaseStructure.TIM_Period = arr;
	TIM_TimeBaseStructure.TIM_ClockDivision = TIM_CKD_DIV1;

	TIM_TimeBaseInit(TIM2, &TIM_TimeBaseStructure);

    TIM_OCInitStructure.TIM_OCMode = TIM_OCMode_PWM1;
	TIM_OCInitStructure.TIM_OutputState = TIM_OutputState_Enable;
	TIM_OCInitStructure.TIM_OCPolarity = TIM_OCPolarity_High;

	TIM_OC1Init(TIM2, &TIM_OCInitStructure);
	TIM_OC1PreloadConfig(TIM2, TIM_OCPreload_Enable);

	TIM_OC2Init(TIM2, &TIM_OCInitStructure);
	TIM_OC2PreloadConfig(TIM2, TIM_OCPreload_Enable);

	TIM_OC3Init(TIM2, &TIM_OCInitStructure);
	TIM_OC3PreloadConfig(TIM2, TIM_OCPreload_Enable);

	TIM_OC4Init(TIM2, &TIM_OCInitStructure);
	TIM_OC4PreloadConfig(TIM2, TIM_OCPreload_Enable);

  	TIM_ARRPreloadConfig(TIM2,ENABLE);

	TIM_Cmd(TIM2, ENABLE);
}
